cliffgraph/FD-ARK/RasPiPico/firmware/fd-ark/title.cpp

/**
 * FD-ARK (RaspberryPiPico firmware)
 * Copyright (c) 2023 Harumakkin.
 * SPDX-License-Identifier: MIT
 */
// https://spdx.org/licenses/

#include "title.h"
const char	*pTITLENAME		= "FD-ARK v1.0.0   ";	// length=16
const int	TITLENAME_SIZE	= 16;
